rmuraglia/menura-kb/docs/img/menura-silhouette.png

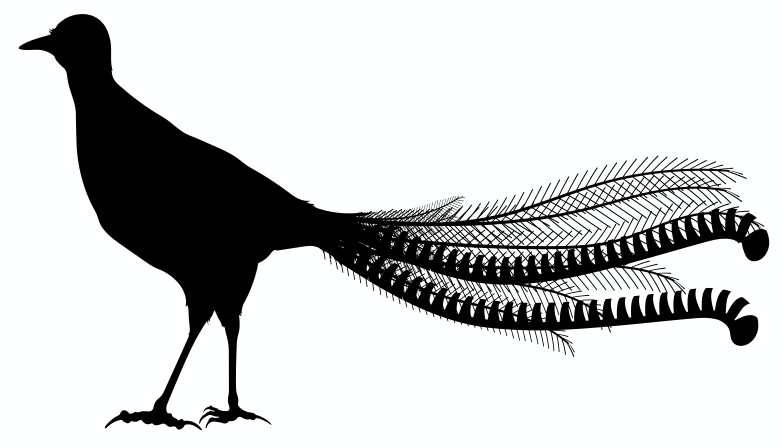
docs/img/menura-silhouette.png
