rmuraglia/menura-kb/case/dxf/components/cutout-pwr.dxf

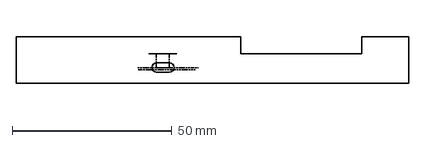
[picture p24: CAD file, 2024-12-25]
case/dxf/components/cutout-pwr.dxf
122.9 x 14.6 mm
