rmuraglia/menura-kb/case/dxf/raw/case_bottom.dxf

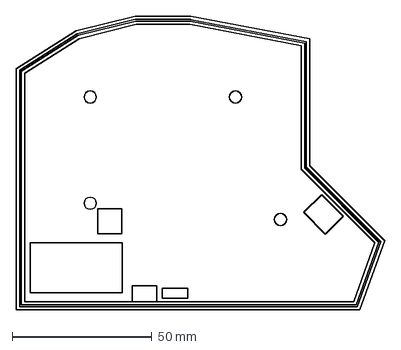
[picture p25: CAD file, 2024-11-23]
case/dxf/raw/case_bottom.dxf
131.9 x 105.2 mm
