rmuraglia/menura-kb/case/dxf/cleaned/case_plate_3x5_3.dxf

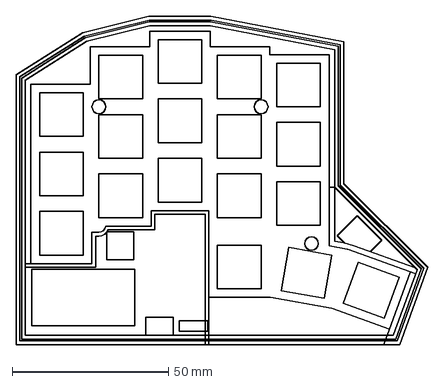
[picture p26: CAD file, 2024-11-24]
case/dxf/cleaned/case_plate_3x5_3.dxf
131.9 x 105.2 mm
