rmuraglia/menura-kb/case/dxf/components/cirque.dxf

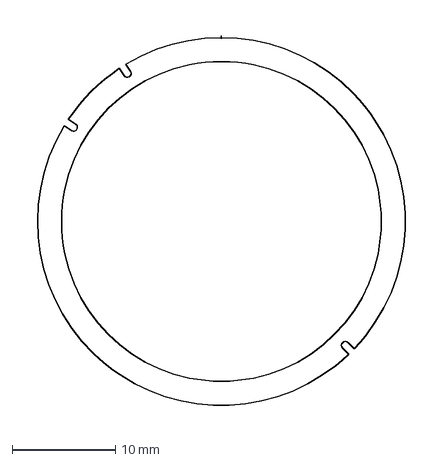
[picture p27: CAD file, 2024-12-25]
case/dxf/components/cirque.dxf
39.4 x 39.4 mm
