rmuraglia/menura-kb/case/dxf/raw/case_plate_23332_2.dxf

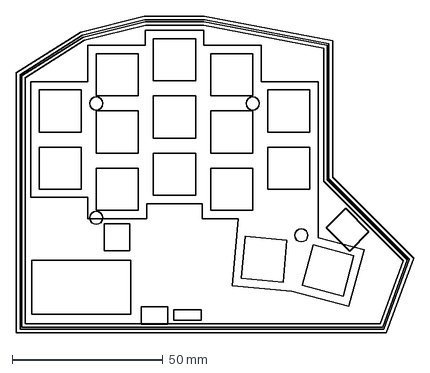
[picture p28: CAD file, 2024-11-23]
case/dxf/raw/case_plate_23332_2.dxf
131.9 x 105.2 mm
