rmuraglia/menura-kb/case/step/wedge_10deg_50mm.step

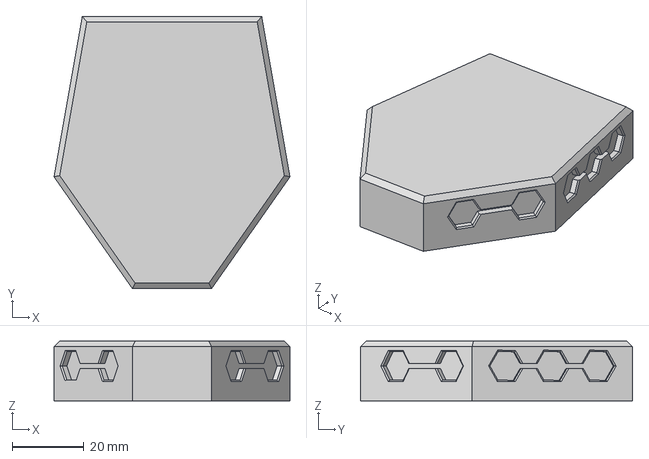
[picture p29: CAD file, 2024-12-22]
case/step/wedge_10deg_50mm.step
65.8 x 75.8 x 16.6 mm
