rmuraglia/menura-kb/case/dxf/cleaned/case_bottom.dxf

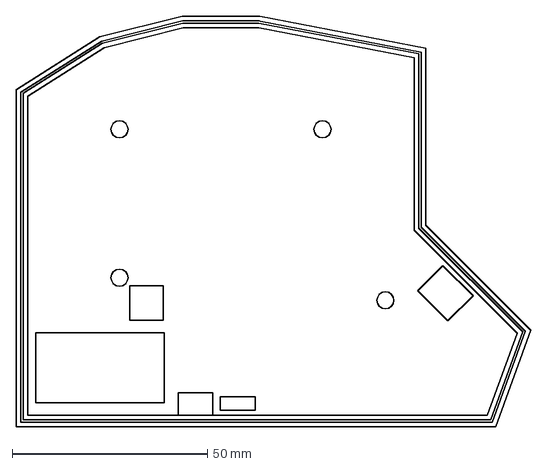
[picture p30: CAD file, 2024-11-23]
case/dxf/cleaned/case_bottom.dxf
131.9 x 105.2 mm
