rmuraglia/menura-kb/case/dxf/raw/case_plate_3x5_3.dxf

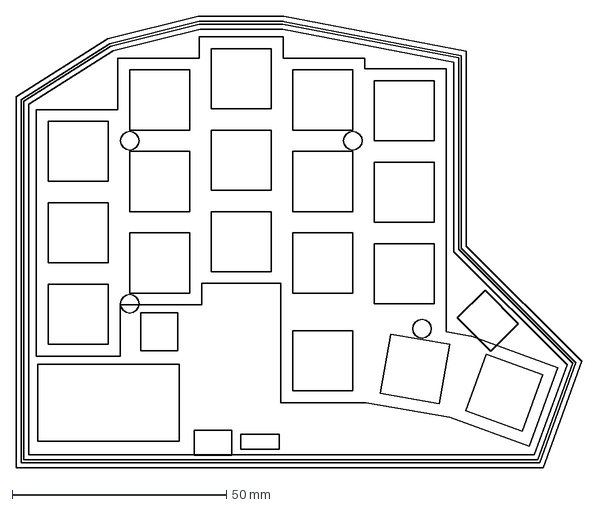
[picture p31: CAD file, 2024-11-23]
case/dxf/raw/case_plate_3x5_3.dxf
131.9 x 105.2 mm
