rmuraglia/menura-kb/case/step/wedge_10deg_34mm.step

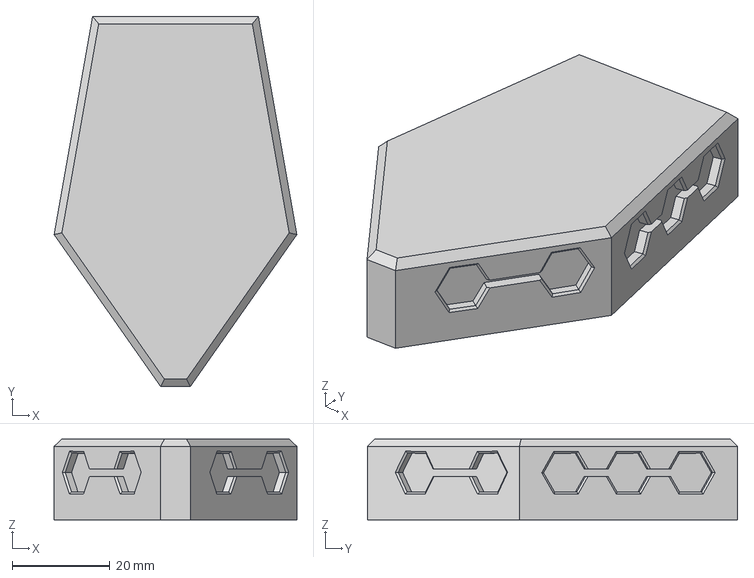
[picture p32: CAD file, 2024-12-22]
case/step/wedge_10deg_34mm.step
49.8 x 75.8 x 16.6 mm
