rmuraglia/menura-kb/case/step/wedge_30deg_0mm.step

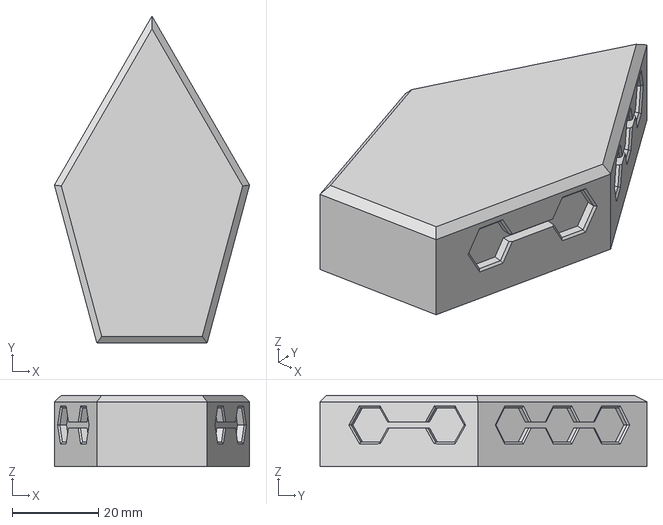
[picture p33: CAD file, 2024-12-22]
case/step/wedge_30deg_0mm.step
45.4 x 76.0 x 16.6 mm
