rmuraglia/menura-kb/case/step/wedge_15deg_18mm.step

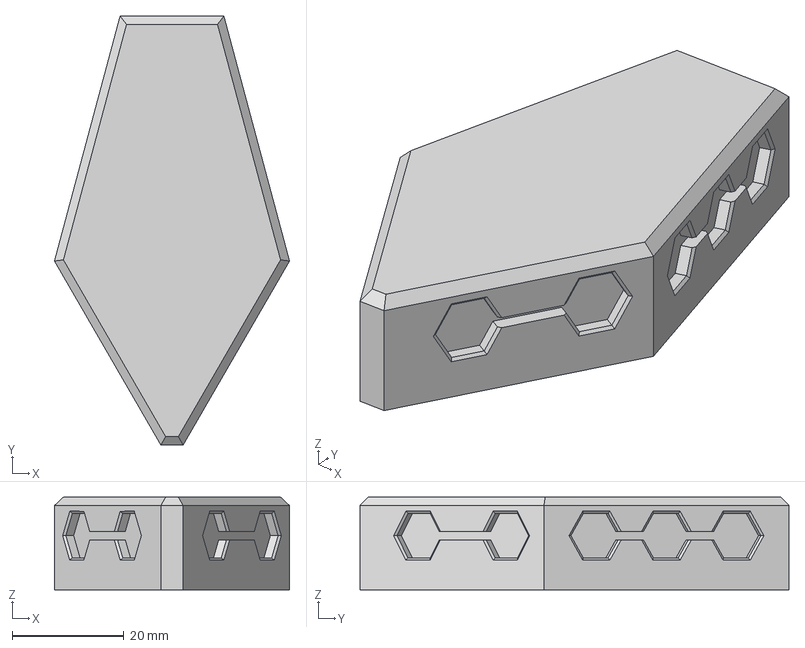
[picture p34: CAD file, 2024-12-22]
case/step/wedge_15deg_18mm.step
42.1 x 76.8 x 16.6 mm
