rmuraglia/menura-kb/case/step/top_3x5_3.step

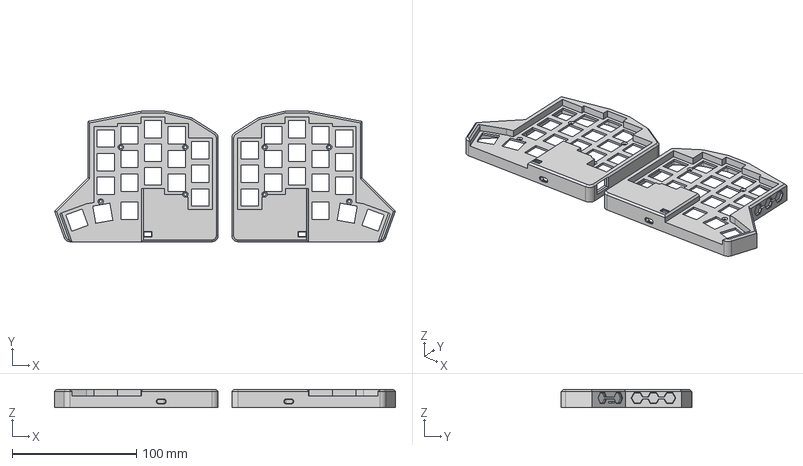
[picture p35: CAD file, 2024-12-22]
case/step/top_3x5_3.step
274.8 x 105.2 x 14.6 mm
