rmuraglia/menura-kb/case/step/top_23332_2.step

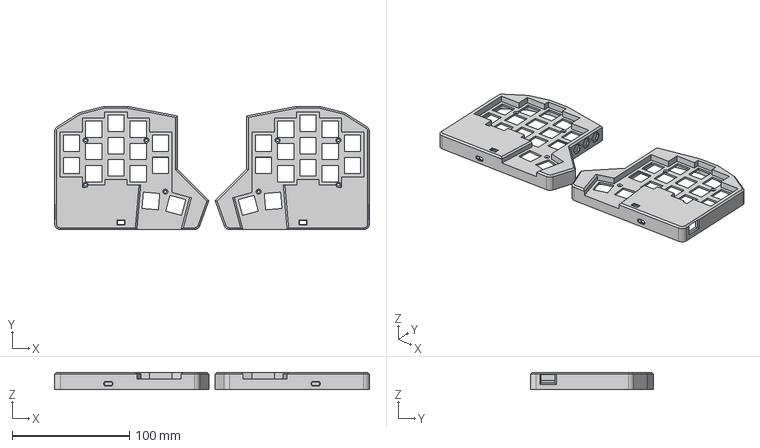
[picture p36: CAD file, 2024-12-21]
case/step/top_23332_2.step
269.0 x 105.2 x 14.6 mm
