rmuraglia/menura-kb/case/step/bottom.step

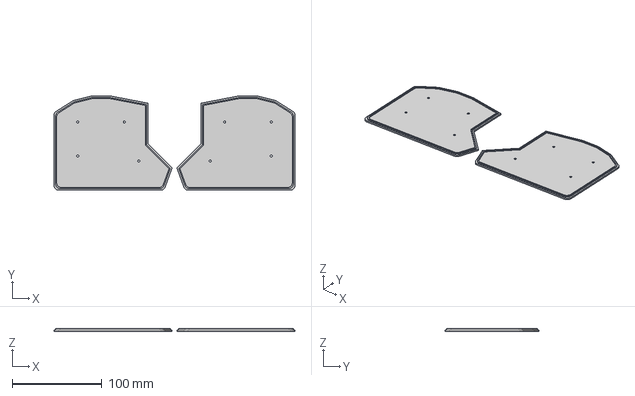
[picture p37: CAD file, 2024-11-23]
case/step/bottom.step
269.0 x 105.2 x 2.80 mm
