rmuraglia/menura-kb/case/stl/bottom_left.stl

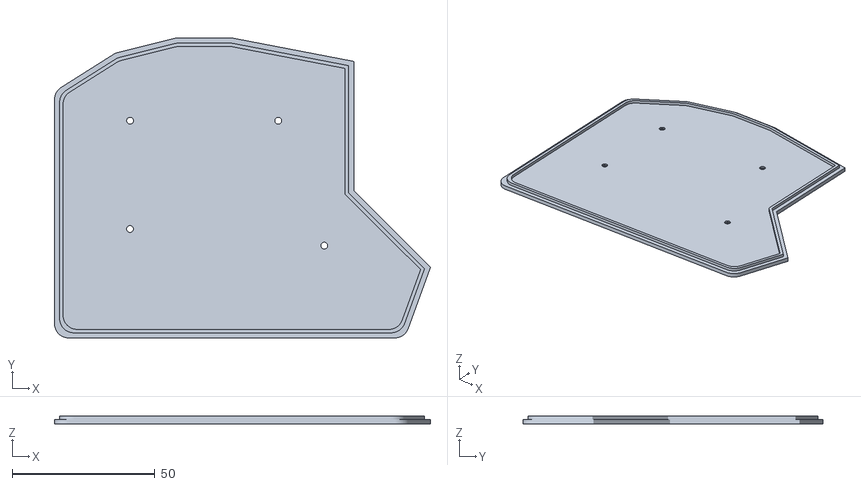
[picture p38: CAD file, 2024-11-23]
case/stl/bottom_left.stl
131.9 x 105.2 x 2.80
